maxksiazka/SR_Project/Electronics/PowerPico.asc

C1: cap; 100n
C2: cap; 220n
D1: schottky; 1N5817
R1: res; 100k
R2: res; 1k
U1: 7805
V1: voltage; 9
Named nets: 0
.tran 1u 1m
