maxksiazka/SR_Project/sumo/src/tcp_typedefs.c

#include "tcp_typedefs.h"
const char* COMMAND_TYPE_STRINGS[] = {
    [COMMAND_ECHO] = "ECHO",
    [COMMAND_STOP] = "STOP",
    [COMMAND_FORWARD] = "FORWARD",
    [COMMAND_BACKWARDS] = "BACKWARD",
    [COMMAND_LEFT] = "LEFT",
    [COMMAND_RIGHT] = "RIGHT",
    [COMMAND_PIVOT_LEFT] = "PIVOT_LEFT",
    [COMMAND_PIVOT_RIGHT] = "PIVOT_RIGHT",
    [COMMAND_UNDEFINED] = "UNDEFINED",
};
bool ECHO_MODE_ENABLED = true;
