maxksiazka/SR_Project/sumo/src/tof_i2c.c

#include "tof_i2c.h"
#include "VL53L0X_pico.h"
#include "hardware/gpio.h"
#include "main.h"
#include "pico/binary_info.h"
#include <hardware/i2c.h>
#include <pico/types.h>

const int XSHUT_PINS[] = {4, 5};

void setup_xshut_pins(void) {
    for (int i = 0; i < 2; i++) {
        gpio_init(XSHUT_PINS[i]);
        gpio_set_dir(XSHUT_PINS[i], GPIO_OUT);
        gpio_put(XSHUT_PINS[i], 0);
    }
    sleep_ms(100);
}

bool tof_set_address(i2c_inst_t* i2c, uint8_t current_addr, uint8_t new_addr) {
    uint8_t buffer[2] = {0x8A, new_addr};

    int ret = i2c_write_blocking(i2c, current_addr, buffer, 2, false);

    return ret == 2;
}

void set_i2c_gpio(void) {
    gpio_set_function(SDA_PIN_0, GPIO_FUNC_I2C);
    gpio_set_function(SDA_PIN_1, GPIO_FUNC_I2C);
    gpio_set_function(SCL_PIN_0, GPIO_FUNC_I2C);
    gpio_set_function(SCL_PIN_1, GPIO_FUNC_I2C);

    gpio_pull_up(SDA_PIN_0);
    gpio_pull_up(SDA_PIN_1);
    gpio_pull_up(SCL_PIN_0);
    gpio_pull_up(SCL_PIN_1);
}

bool initSingleTof(i2c_inst_t* i2c, uint8_t addr) {
    int rev, model;
    if (tofInit(i2c, addr, 0) != 1) {
        DEBUG_printf("VL53L0X initialization failed at %u, address 0x%d.\n",
                     i2c_hw_index(i2c), addr);
        return false;
    }
    sleep_ms(5);
    tofGetModel(i2c, addr, &model, &rev);
    DEBUG_printf("Model ID: %d\n", model);
    DEBUG_printf("Revision ID: %d\n", rev);
    DEBUG_printf("VL53L0X initialized on address %d\n", addr);
    return true;
}

bool i2c_start(void) {
    int model, rev;

    i2c_init(I2C_PORT_0, 400 * 1000);
    i2c_init(I2C_PORT_1, 400 * 1000);
    set_i2c_gpio();
    bi_decl(bi_2pins_with_func(SDA_PIN_0, SCL_PIN_0, GPIO_FUNC_I2C));
    bi_decl(bi_2pins_with_func(SDA_PIN_1, SCL_PIN_1, GPIO_FUNC_I2C));
    setup_xshut_pins();

    gpio_put(XSHUT_PINS[0], 0);
    gpio_put(XSHUT_PINS[1], 0);

    sleep_ms(10);

    tof_set_address(I2C_PORT_0, DEF_ADDR, NEW_ADDR);
    tof_set_address(I2C_PORT_1, DEF_ADDR, NEW_ADDR);

    gpio_put(XSHUT_PINS[0], 1);
    gpio_put(XSHUT_PINS[1], 1);
    sleep_ms(10);

    if (!initSingleTof(I2C_PORT_0, DEF_ADDR))
        return false;

    if (!initSingleTof(I2C_PORT_0, NEW_ADDR))
        return false;

    if (!initSingleTof(I2C_PORT_1, DEF_ADDR))
        return false;

    if (!initSingleTof(I2C_PORT_1, NEW_ADDR))
        return false;

    return true;
}
